jakeson21/Roadrunner-TM4C123G/board-art/my_roadrunner.png

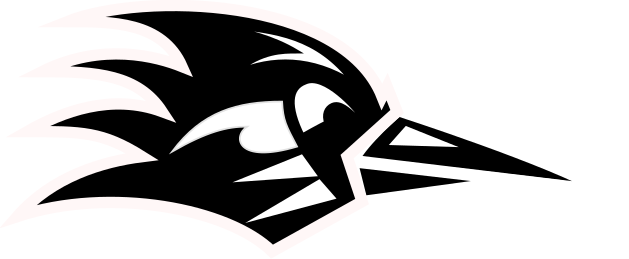
board-art/my_roadrunner.png
