jakeson21/Roadrunner-TM4C123G/images/Arduino_Leo_Tiva_HiFi_ortho_osh.png

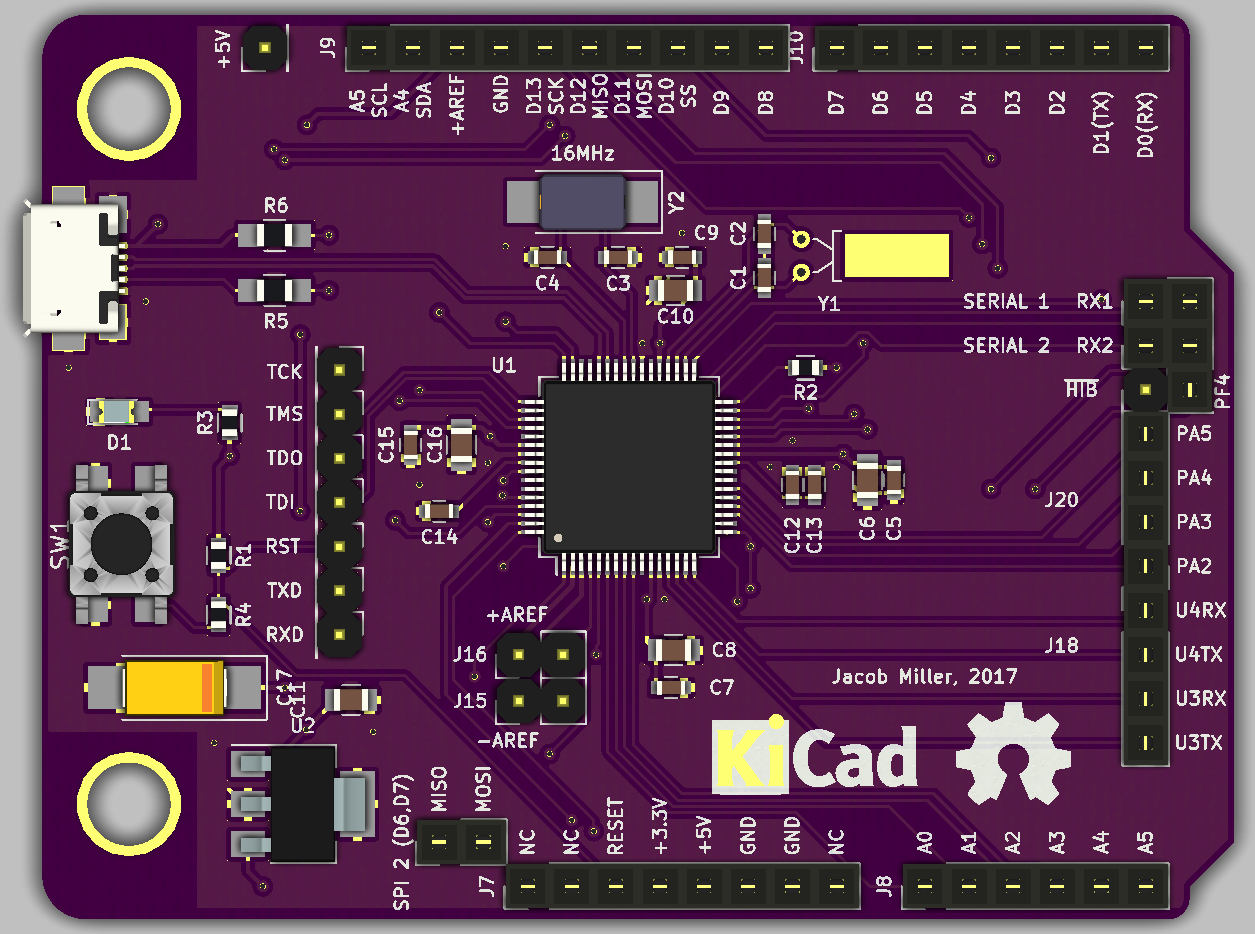
images/Arduino_Leo_Tiva_HiFi_ortho_osh.png
