jakeson21/Roadrunner-TM4C123G/images/Arduino_Leo_Tiva_HiFi_ortho_osh_noshadow.jpg

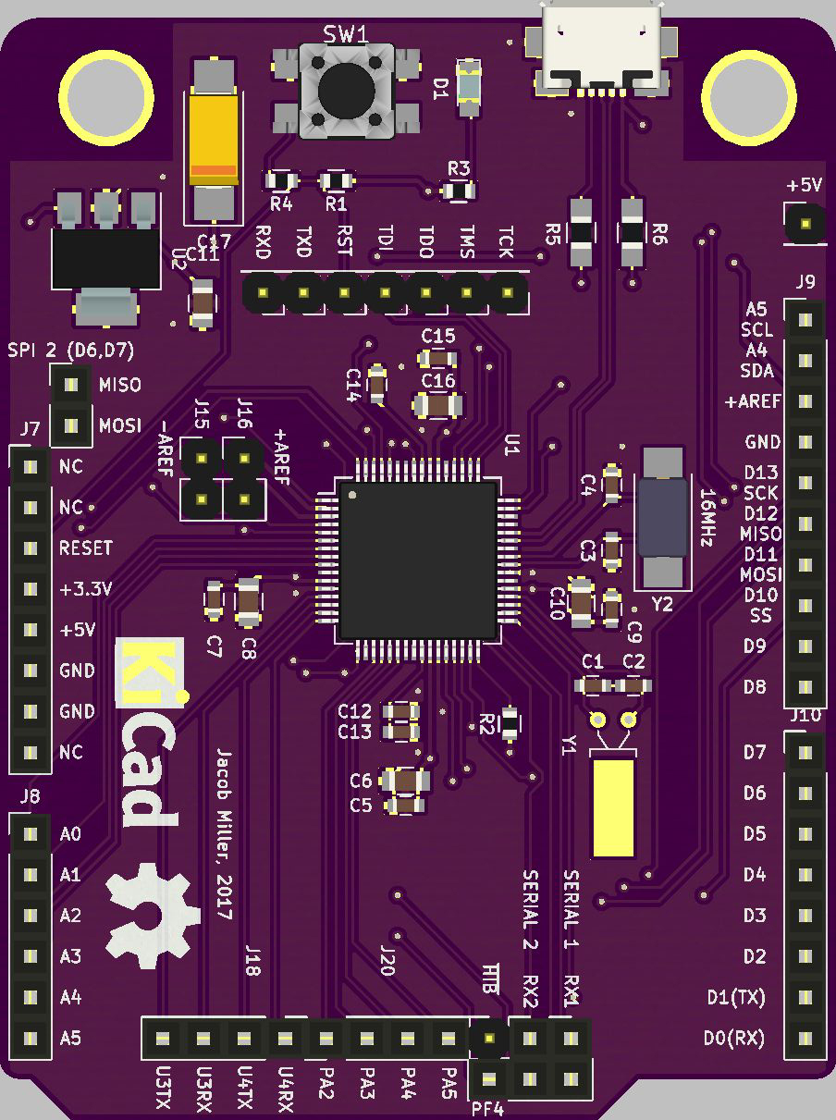
images/Arduino_Leo_Tiva_HiFi_ortho_osh_noshadow.jpg
