jakeson21/Roadrunner-TM4C123G/images/Capture.PNG

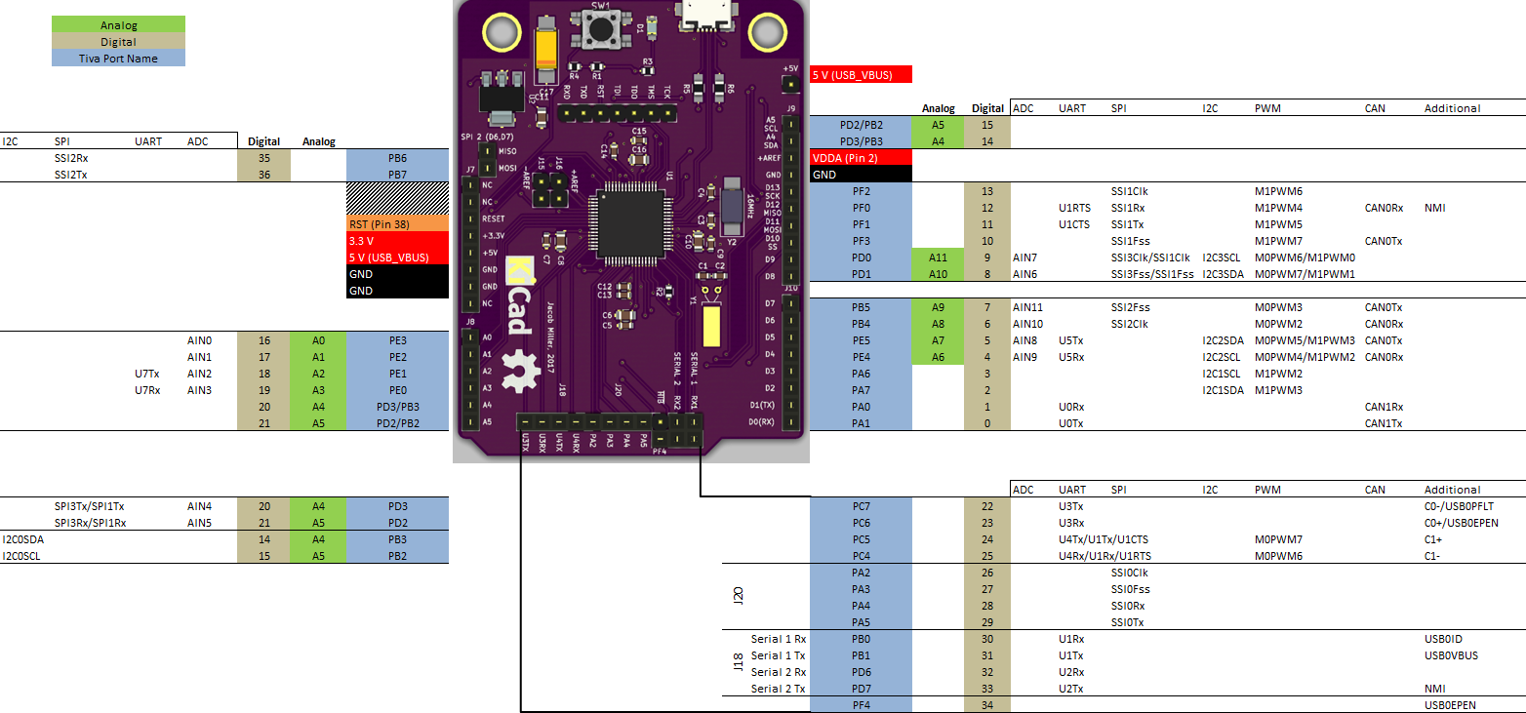
images/Capture.PNG
