jakeson21/Roadrunner-TM4C123G/images/Full_speed_digital.PNG

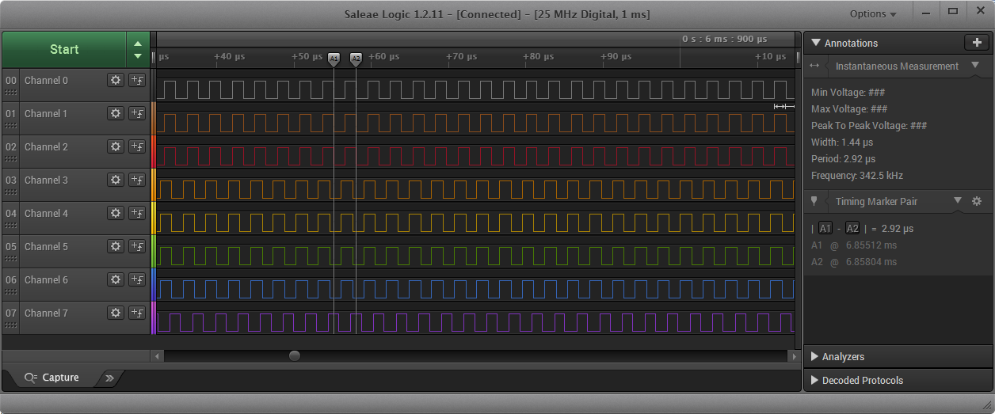
images/Full_speed_digital.PNG
