jakeson21/Roadrunner-TM4C123G/images/IMGP2365.jpg

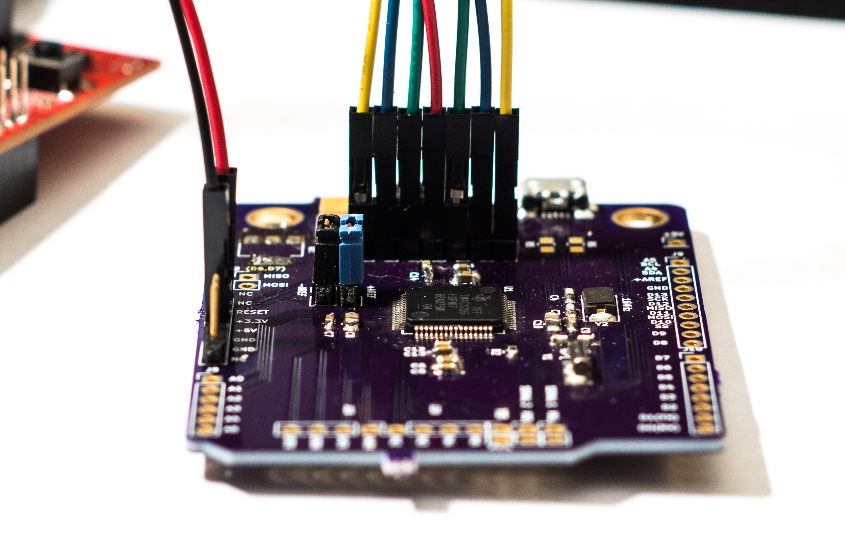
images/IMGP2365.jpg
