jakeson21/Roadrunner-TM4C123G/images/IMGP2377.jpg

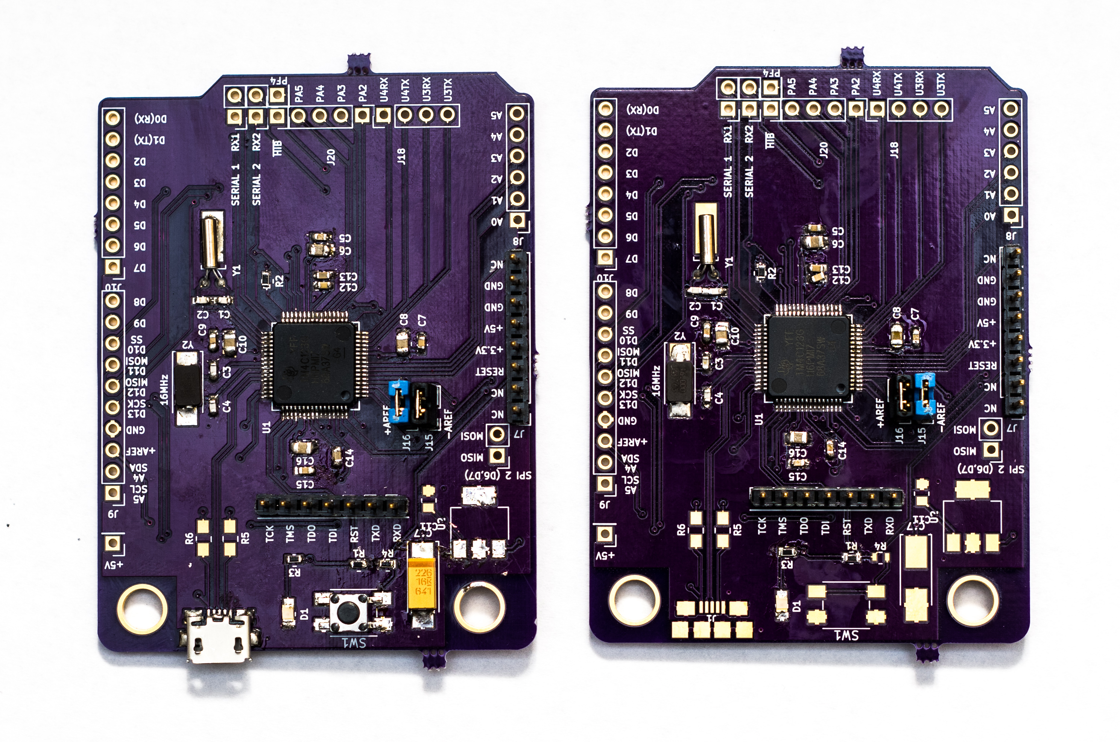
images/IMGP2377.jpg
