jakeson21/Roadrunner-TM4C123G/images/LaunchPads-LM4F-TM4C-—-Pins-Maps-11-32.jpeg

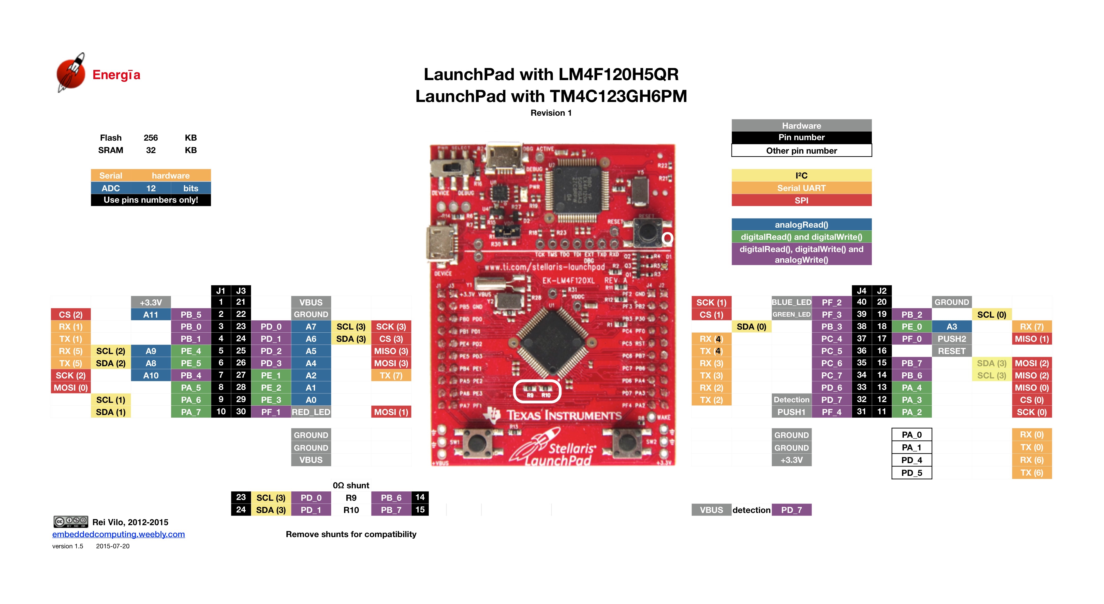
images/LaunchPads-LM4F-TM4C-—-Pins-Maps-11-32.jpeg
