jakeson21/Roadrunner-TM4C123G/images/LayoutCapture.PNG

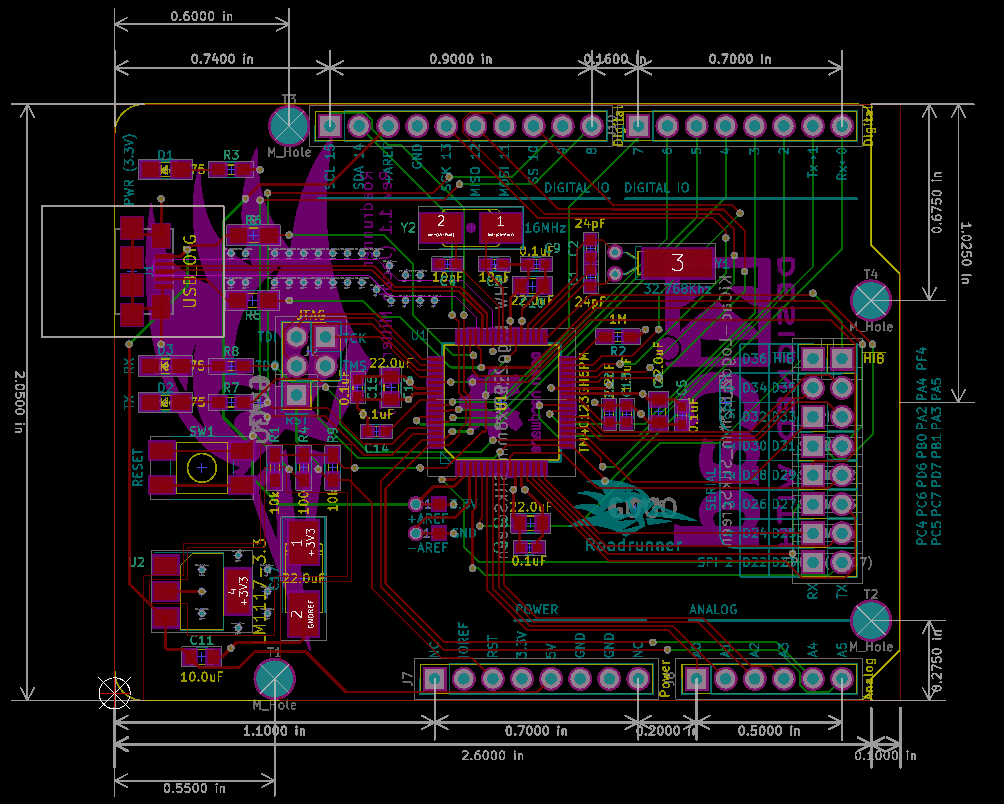
images/LayoutCapture.PNG
