jakeson21/Roadrunner-TM4C123G/images/osh-park-bottom.png

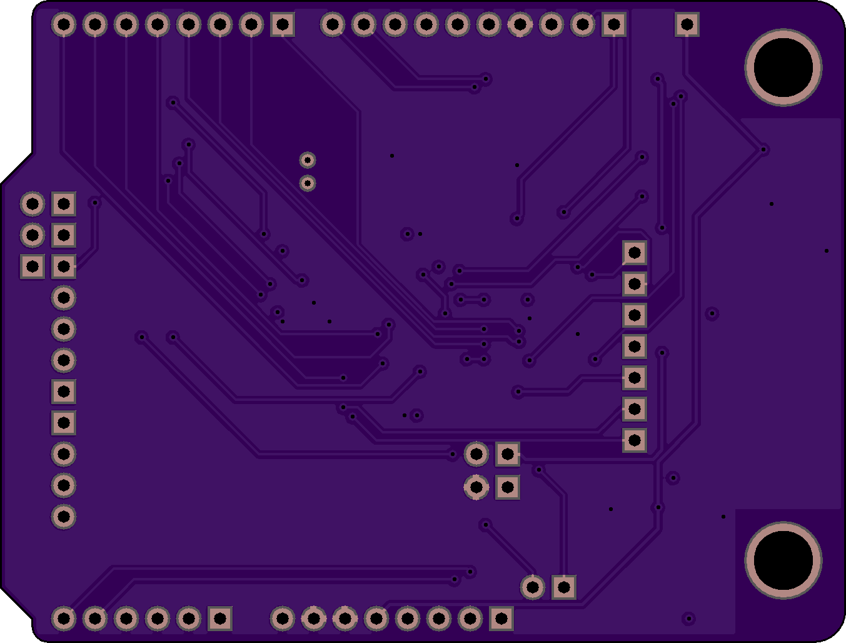
images/osh-park-bottom.png
