jakeson21/Roadrunner-TM4C123G/images/Roadrunner_45.png

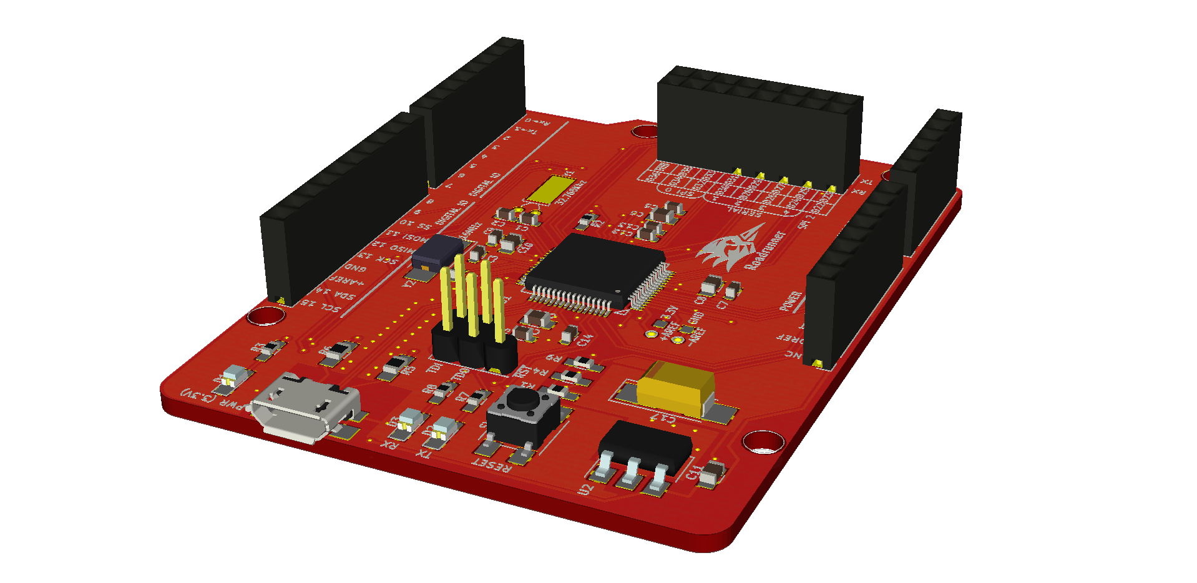
images/Roadrunner_45.png
