jakeson21/Roadrunner-TM4C123G/images/Roadrunner_bottom_v1.1.png

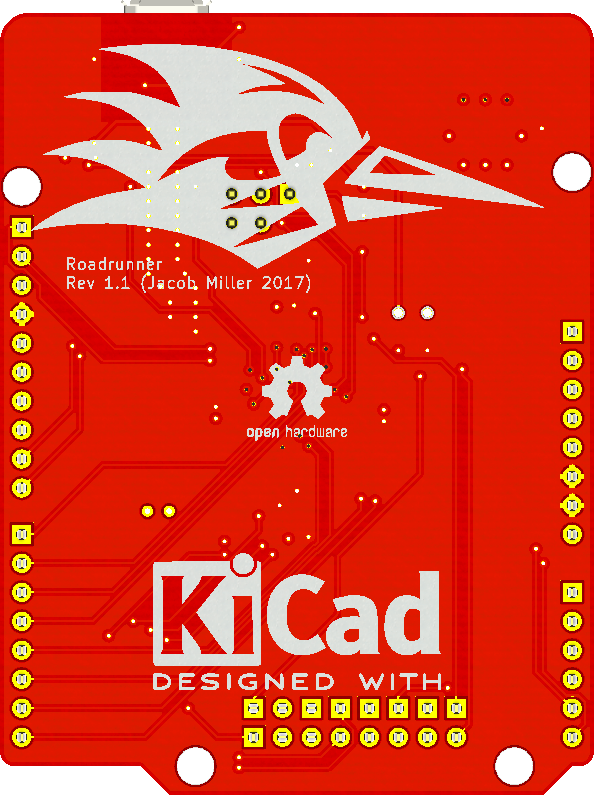
images/Roadrunner_bottom_v1.1.png
